danfoisy/flicker/docs/images/20191109_113527.jpg

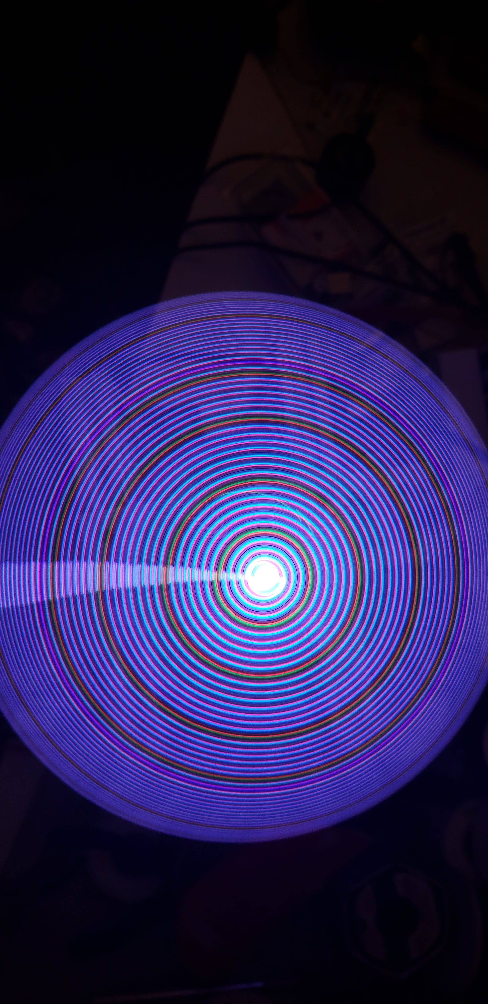
docs/images/20191109_113527.jpg
