danfoisy/flicker/prints/slots v1.stl

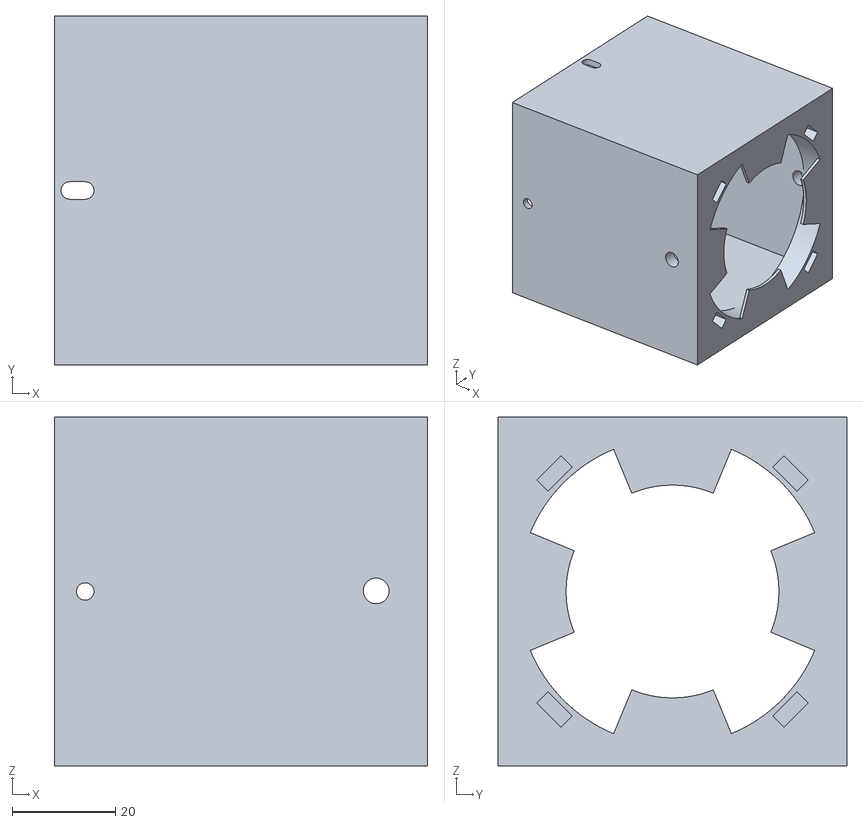
[picture p44: CAD file, 2020-12-12]
prints/slots v1.stl
72.5 x 67.8 x 67.8
