danfoisy/flicker/prints/motor magnet.stl

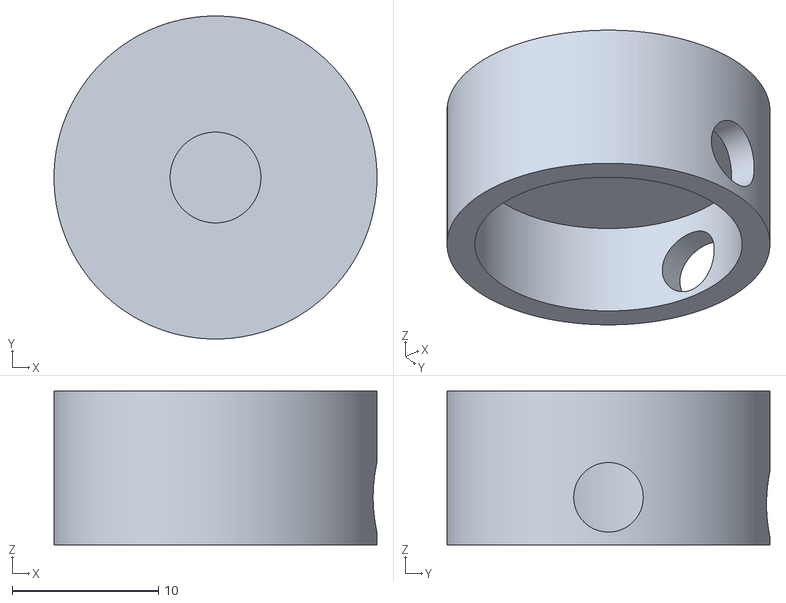
[picture p45: CAD file, 2020-12-12]
prints/motor magnet.stl
22.0 x 22.0 x 10.5
