danfoisy/flicker/prints/stand.stl

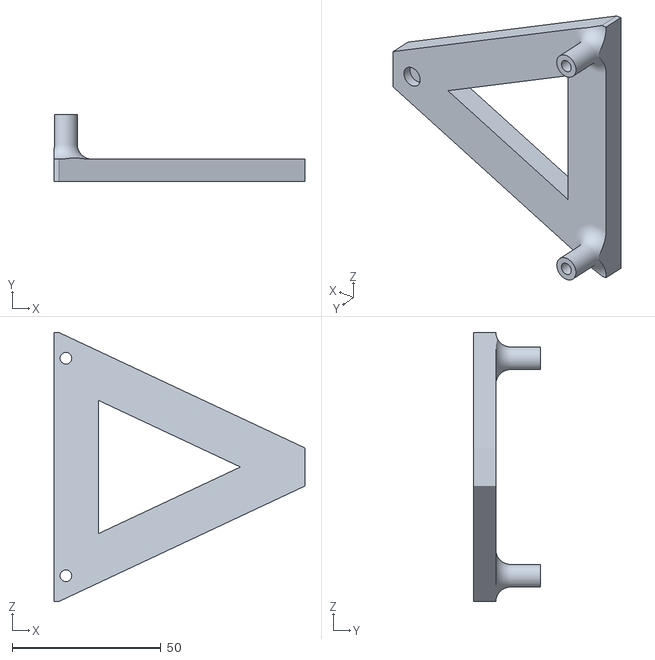
[picture p46: CAD file, 2020-12-12]
prints/stand.stl
84.3 x 22.5 x 90.4
