danfoisy/flicker/prints/counterweight.stl

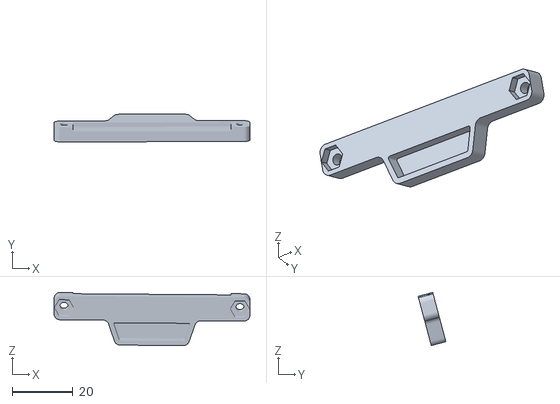
[picture p47: CAD file, 2020-12-12]
prints/counterweight.stl
64.6 x 9.18 x 17.5
