danfoisy/flicker/prints/finger holderx4a.stl

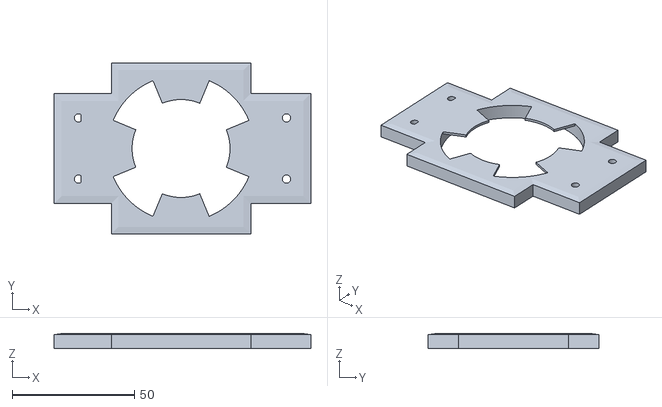
[picture p48: CAD file, 2020-12-12]
prints/finger holderx4a.stl
105.0 x 70.0 x 6.00
