danfoisy/flicker/prints/pcb_coupler v2.stl

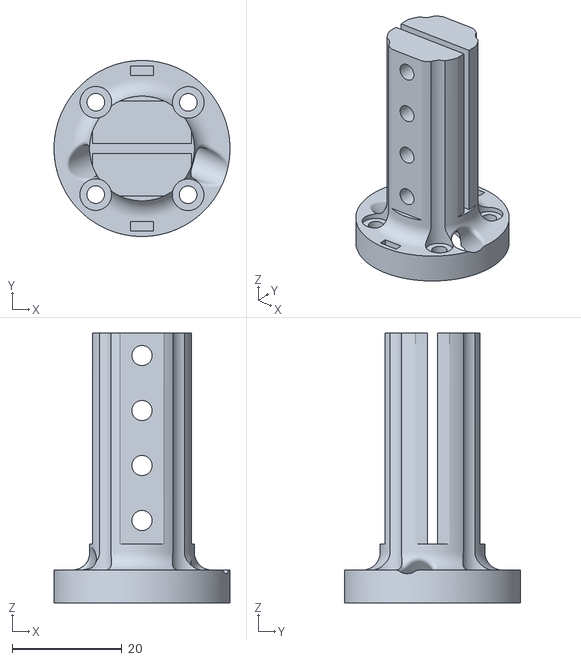
[picture p49: CAD file, 2020-12-12]
prints/pcb_coupler v2.stl
32.0 x 32.0 x 49.1
