danfoisy/flicker/prints/top spacer.stl

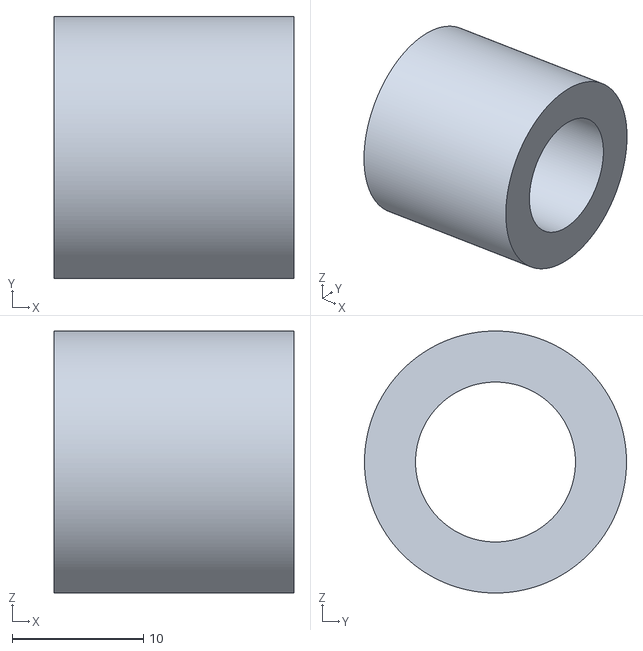
[picture p50: CAD file, 2020-12-12]
prints/top spacer.stl
18.3 x 20.0 x 20.0
