danfoisy/flicker/prints/magholder_retainer.stl

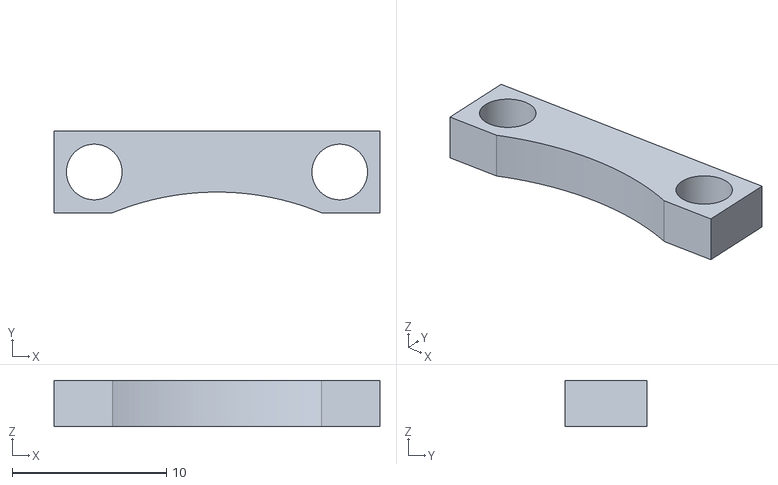
[picture p51: CAD file, 2020-12-12]
prints/magholder_retainer.stl
21.1 x 5.30 x 3.00
