danfoisy/flicker/prints/timing.stl

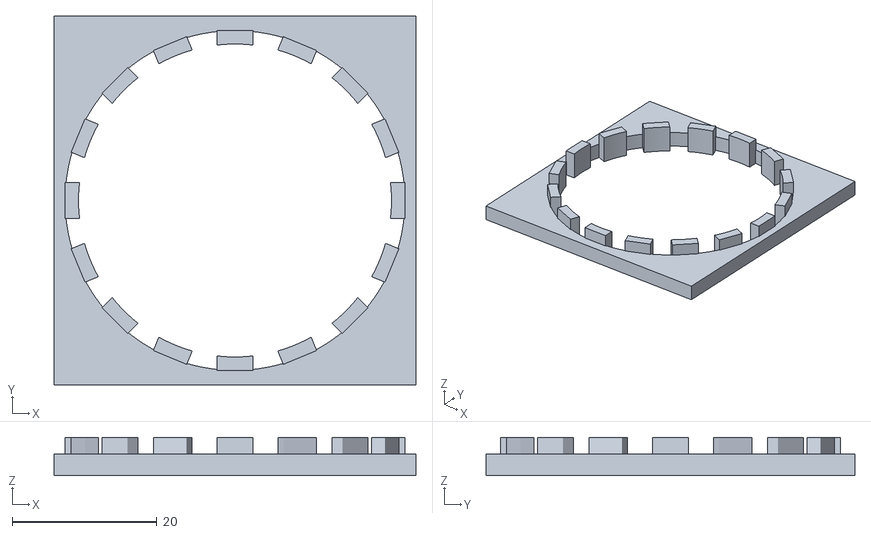
[picture p52: CAD file, 2020-12-12]
prints/timing.stl
50.0 x 51.0 x 5.28
