danfoisy/flicker/prints/bearing support.stl

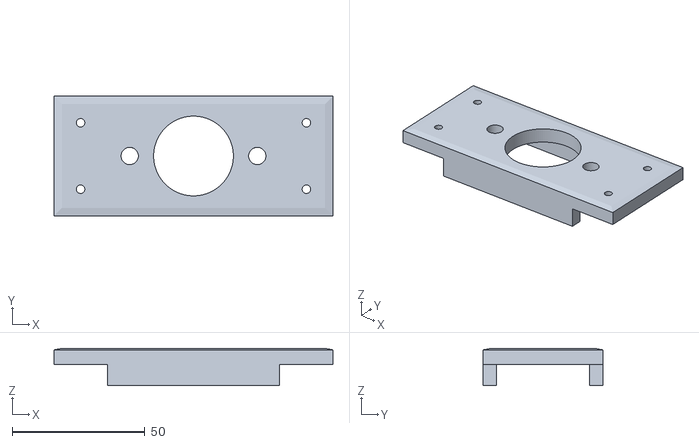
[picture p53: CAD file, 2020-12-12]
prints/bearing support.stl
105.0 x 45.0 x 14.0
