danfoisy/flicker/prints/motor mount.stl

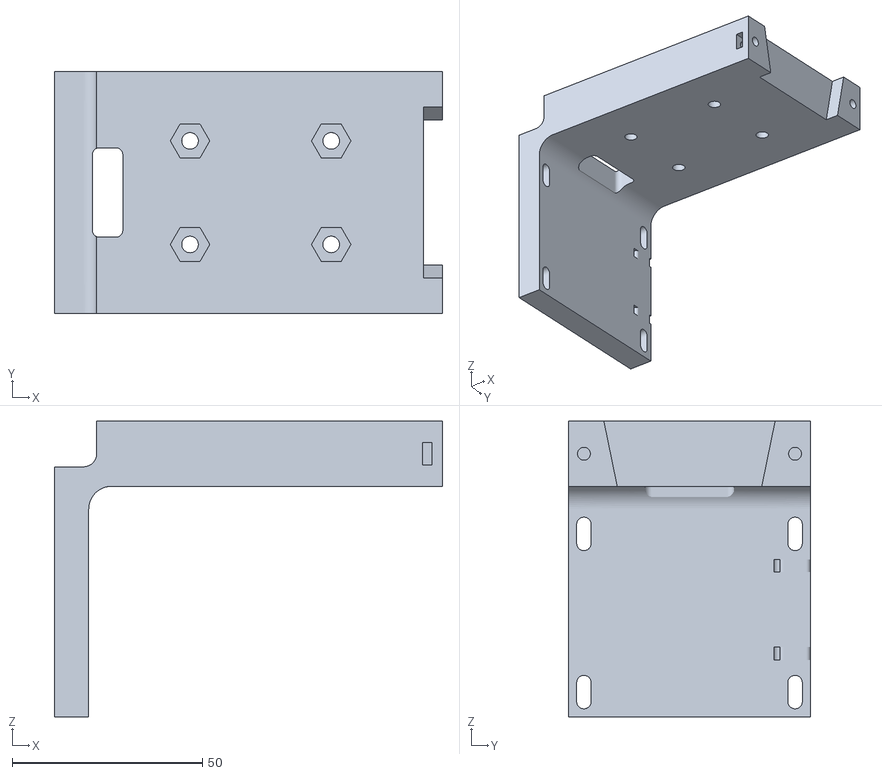
[picture p54: CAD file, 2020-12-12]
prints/motor mount.stl
102.0 x 63.5 x 77.7
