danfoisy/flicker/prints/housing top.stl

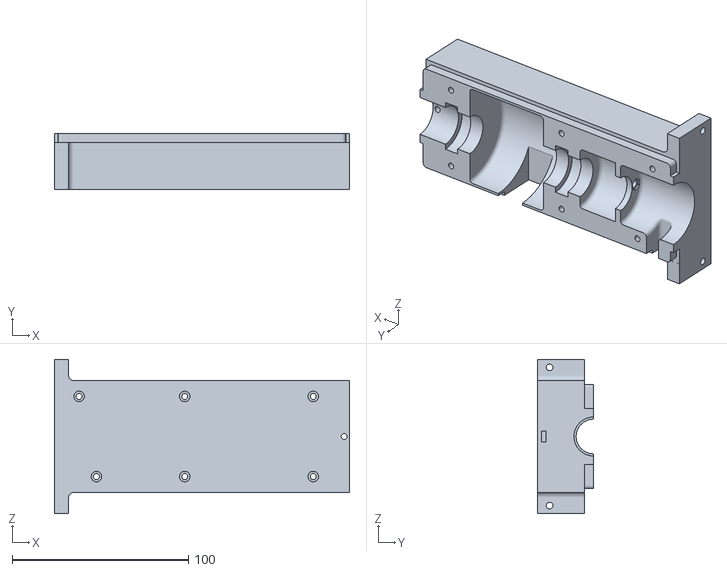
[picture p55: CAD file, 2020-12-12]
prints/housing top.stl
167.5 x 31.8 x 87.5
