danfoisy/flicker/prints/bottom spacer.stl

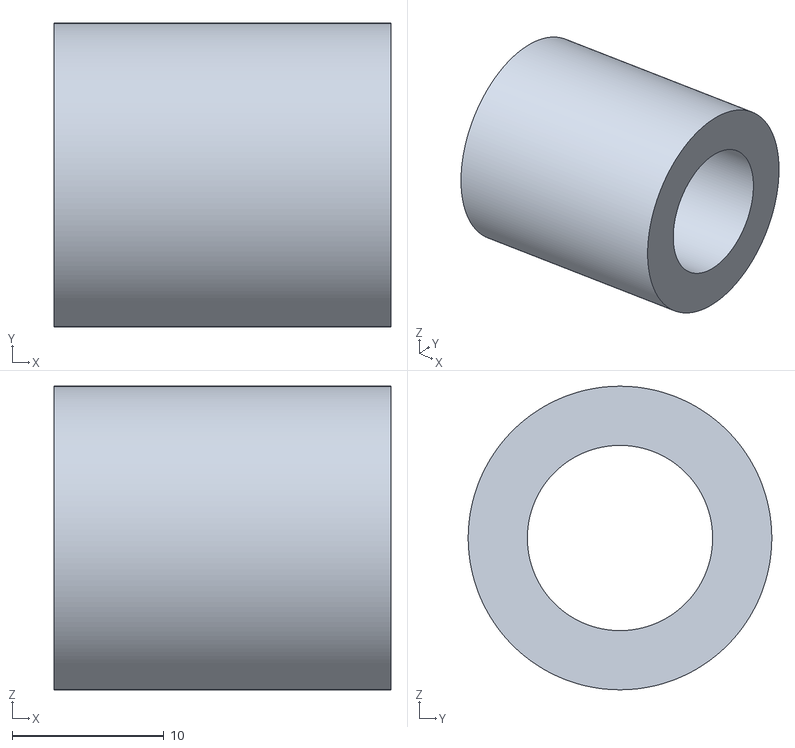
[picture p56: CAD file, 2020-12-12]
prints/bottom spacer.stl
22.2 x 20.0 x 20.0
