danfoisy/flicker/prints/slots.stl

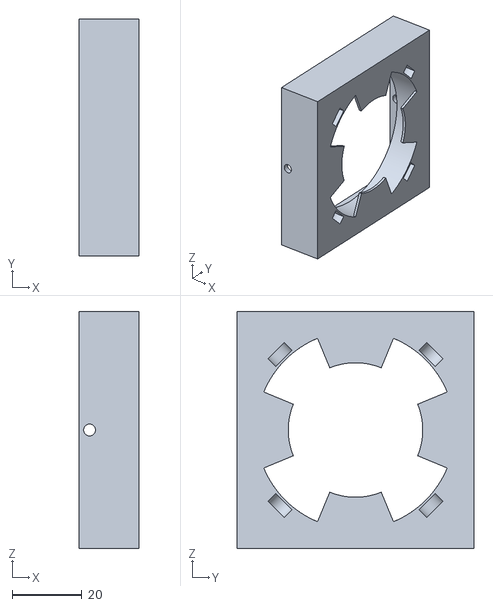
[picture p57: CAD file, 2020-12-12]
prints/slots.stl
17.1 x 67.8 x 67.8
