danfoisy/flicker/prints/finger holder.stl

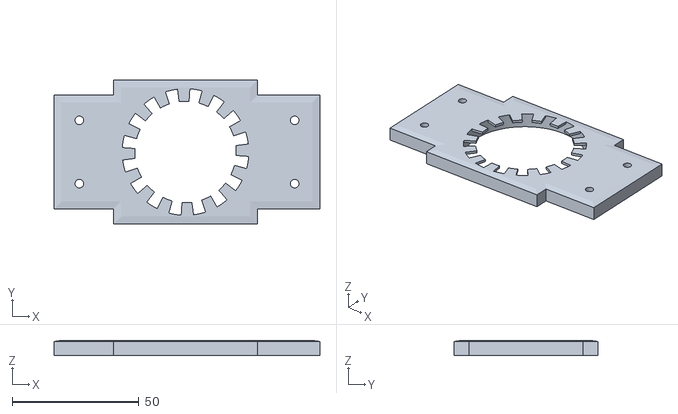
[picture p58: CAD file, 2020-12-12]
prints/finger holder.stl
105.0 x 57.0 x 6.00
