danfoisy/flicker/prints/rpm sensor holder.stl

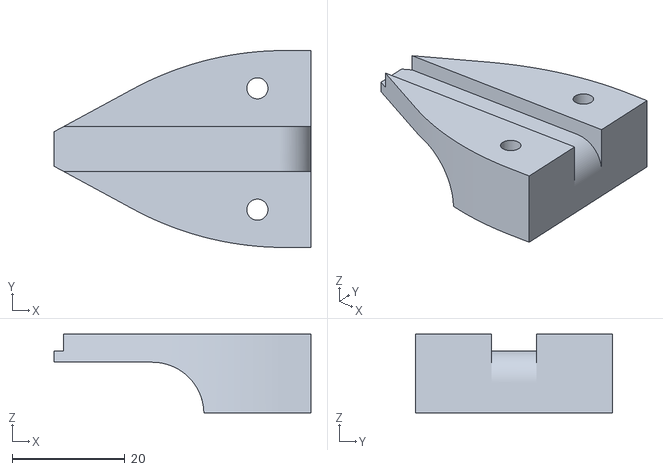
[picture p59: CAD file, 2020-12-12]
prints/rpm sensor holder.stl
45.7 x 35.0 x 14.0
