danfoisy/flicker/prints/housing bottom.stl

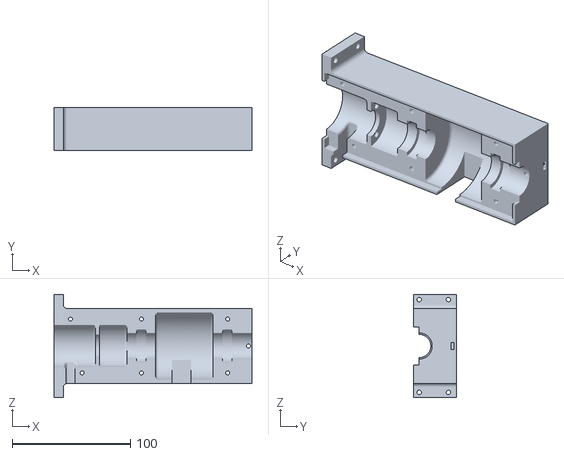
[picture p60: CAD file, 2020-12-12]
prints/housing bottom.stl
167.5 x 36.8 x 87.5
