danfoisy/flicker/prints/sensor mnt.stl

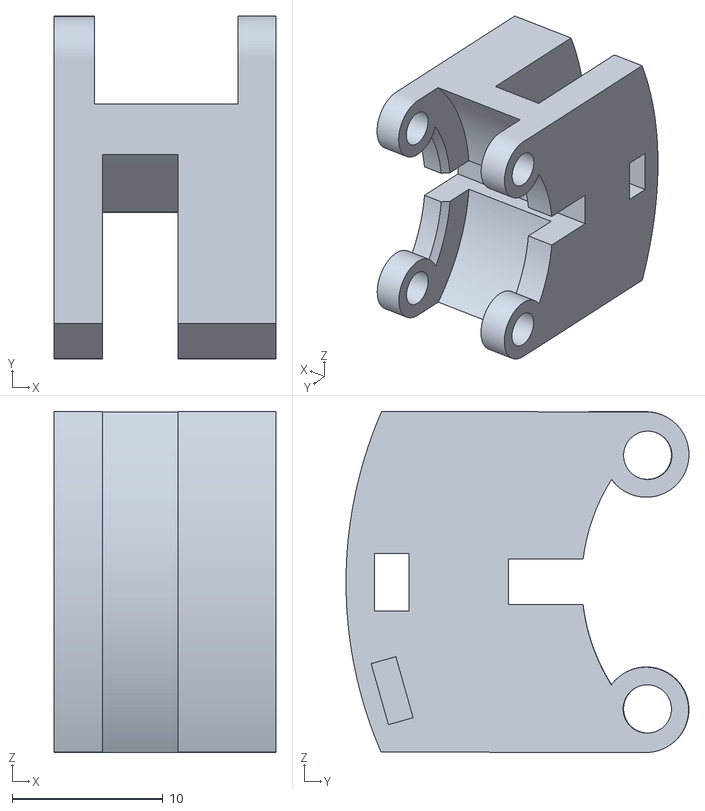
[picture p61: CAD file, 2020-12-12]
prints/sensor mnt.stl
14.7 x 22.7 x 22.6
