danfoisy/flicker/prints/weight top.stl

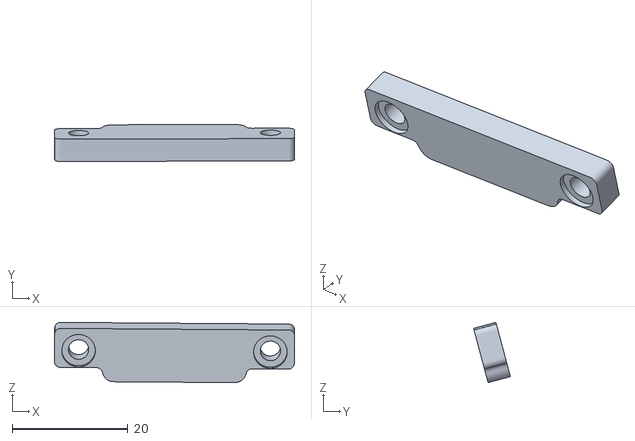
[picture p62: CAD file, 2020-12-12]
prints/weight top.stl
41.4 x 6.37 x 10.4
