danfoisy/flicker/prints/sliprng support.stl

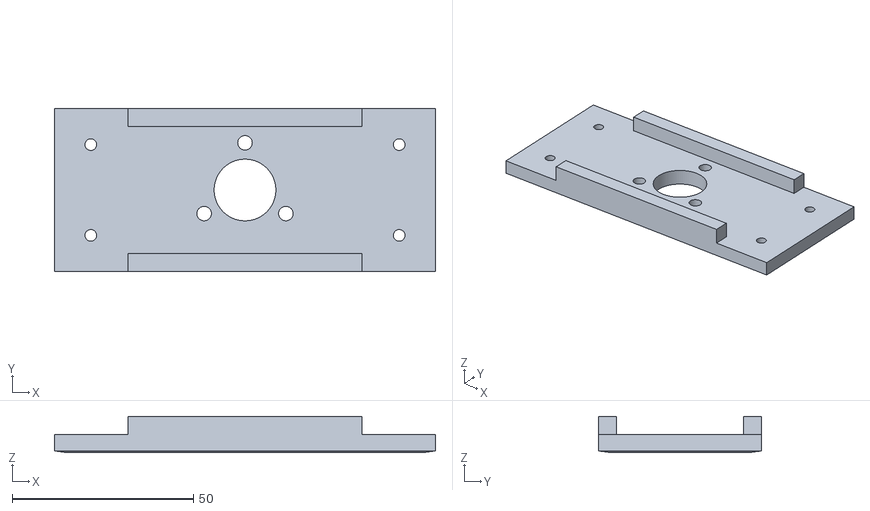
[picture p63: CAD file, 2020-12-12]
prints/sliprng support.stl
105.0 x 45.0 x 10.00
