danfoisy/flicker/prints/diffuser.stl

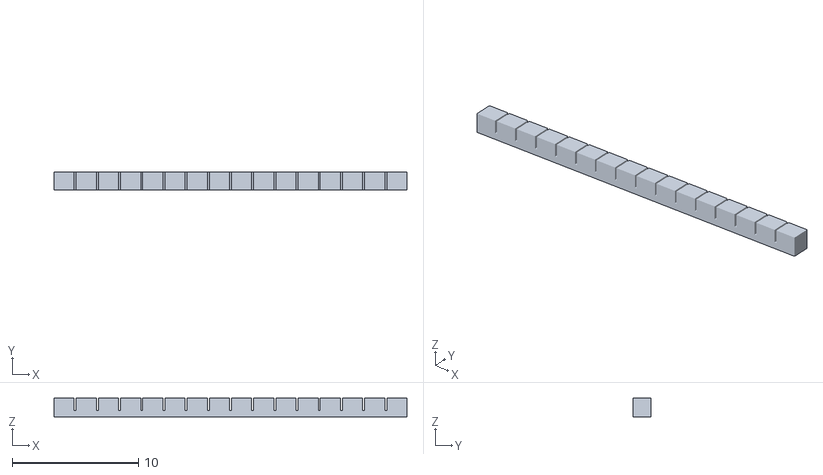
[picture p64: CAD file, 2020-12-12]
prints/diffuser.stl
28.0 x 1.41 x 1.50
