danfoisy/flicker/prints/top bracket.stl

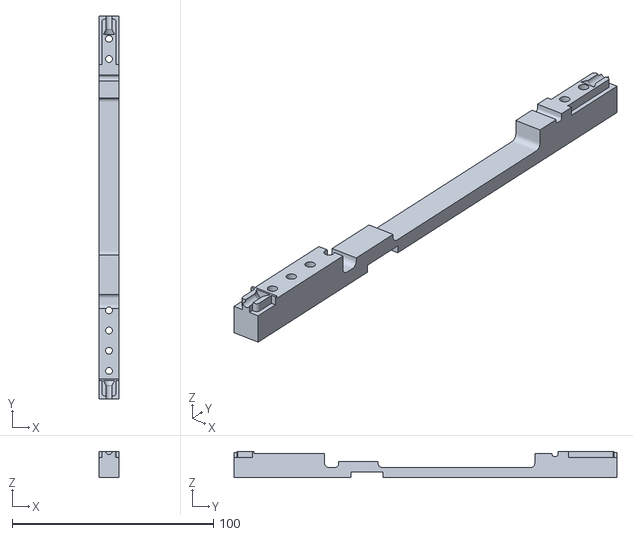
[picture p65: CAD file, 2020-12-12]
prints/top bracket.stl
10.0 x 190.1 x 12.9
