danfoisy/flicker/prints/box top.stl

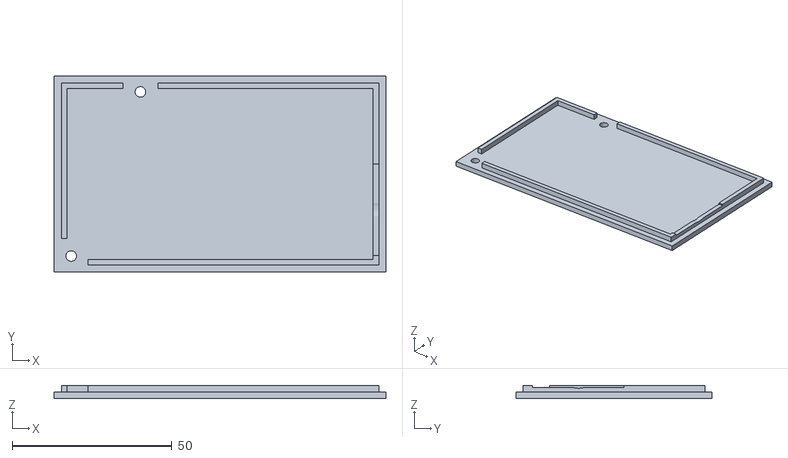
[picture p66: CAD file, 2020-12-12]
prints/box top.stl
103.9 x 61.3 x 4.00
