danfoisy/flicker/prints/magnet holder 2.stl

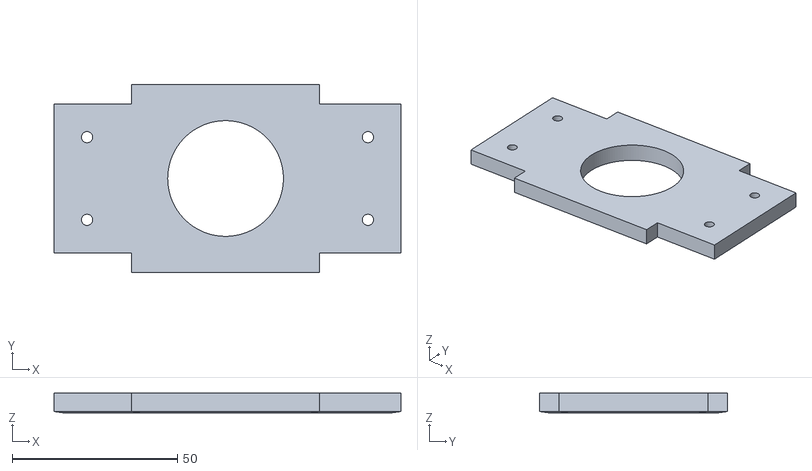
[picture p67: CAD file, 2020-12-12]
prints/magnet holder 2.stl
105.0 x 57.0 x 6.00
