danfoisy/flicker/prints/timing1.stl

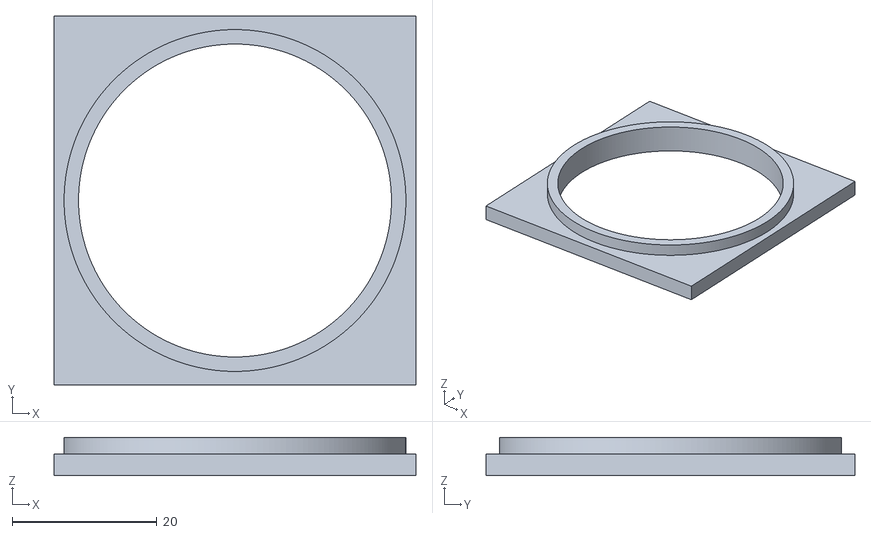
[picture p68: CAD file, 2020-12-12]
prints/timing1.stl
50.0 x 51.0 x 5.28
