danfoisy/flicker/board/flicker/200-memory.sch

## KiCad design board/flicker/200-memory.sch (2020-12-05)

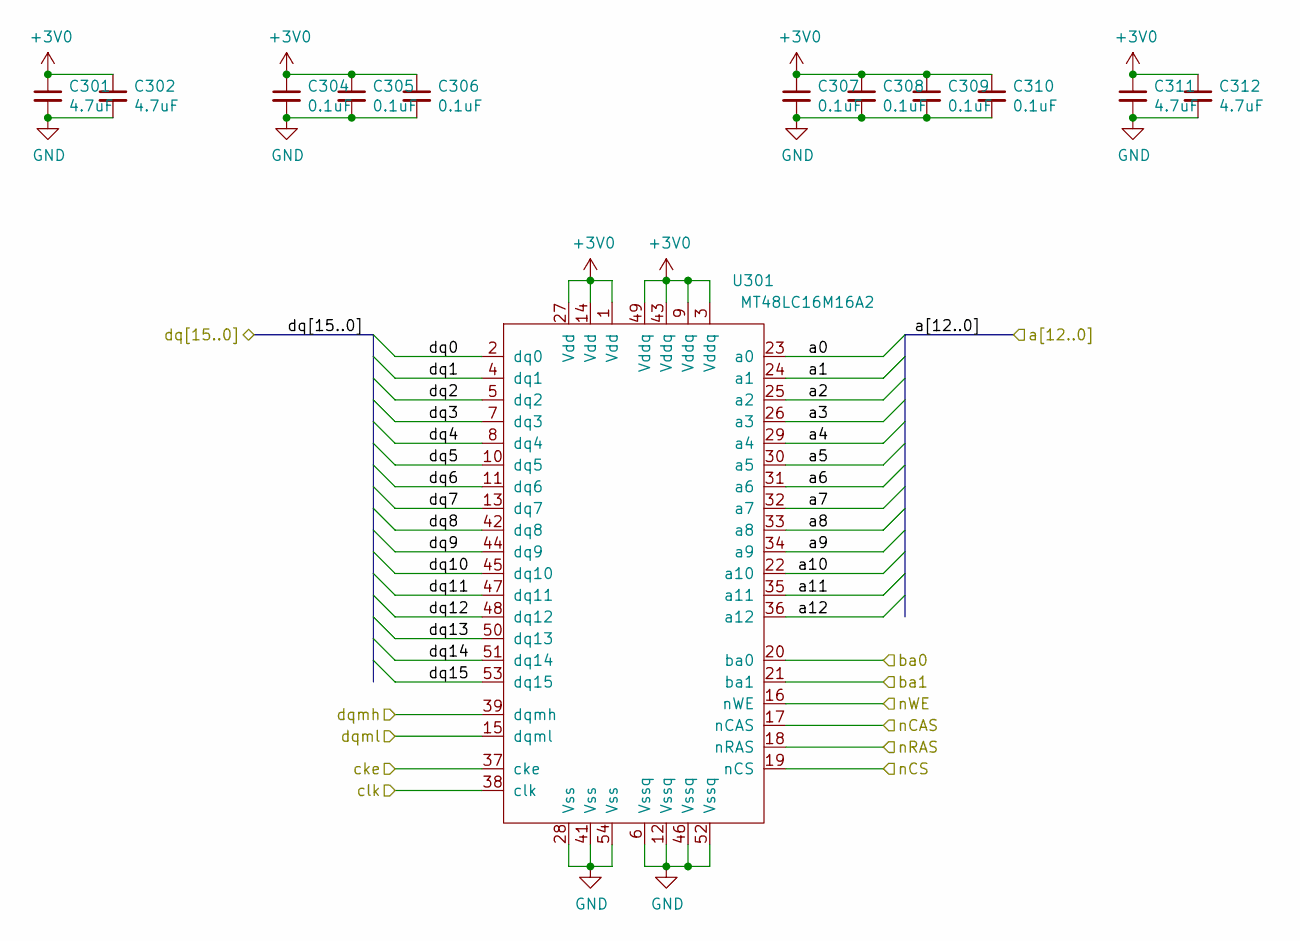
[picture p91: schematic 200-memory.sch]

Parts:
C301, C302, C311, C312: 4.7uF; C_0603_1608Metric_Pad1.05x0.95mm_HandSolder
C304, C305, C306, C307, C308, C309, C310: 0.1uF; C_0402_1005Metric_HandSolder
U301: MT48LC16M16A2; TSOP-II-54_22.2x10.16mm_P0.8mm

Connections:
+3V0: C301.1, C302.1, C304.1, C305.1, C306.1, C307.1, C308.1, C309.1, C310.1, C311.1, C312.1, U301.1 (Vdd), U301.3 (Vddq), U301.9 (Vddq), U301.14 (Vdd), U301.27 (Vdd~), U301.43 (Vddq), U301.49 (Vddq)
GND: C301.2, C302.2, C304.2, C305.2, C306.2, C307.2, C308.2, C309.2, C310.2, C311.2, C312.2, U301.6 (Vssq), U301.12 (Vssq), U301.28 (Vss), U301.41 (Vss), U301.46 (Vssq), U301.52 (Vssq), U301.54 (Vss)
a0: U301.23 (a0~)
a1: U301.24 (a1)
a2: U301.25 (a2)
a3: U301.26 (a3)
a4: U301.29 (a4)
a5: U301.30 (a5)
a6: U301.31 (a6)
a7: U301.32 (a7)
a8: U301.33 (a8)
a9: U301.34 (a9)
a10: U301.22 (a10~)
a11: U301.35 (a11)
a12: U301.36 (a12)
ba0: U301.20 (ba0~)
ba1: U301.21 (ba1)
cke: U301.37 (cke)
clk: U301.38 (clk)
dq0: U301.2 (dq0)
dq1: U301.4 (dq1)
dq2: U301.5 (dq2)
dq3: U301.7 (dq3)
dq4: U301.8 (dq4)
dq5: U301.10 (dq5)
dq6: U301.11 (dq6)
dq7: U301.13 (dq7)
dq8: U301.42 (dq8)
dq9: U301.44 (dq9)
dq10: U301.45 (dq10)
dq11: U301.47 (dq11)
dq12: U301.48 (dq12)
dq13: U301.50 (dq13)
dq14: U301.51 (dq14)
dq15: U301.53 (dq15)
dqmh: U301.39 (dqmh)
dqml: U301.15 (dqml)
nCAS: U301.17 (nCAS)
nCS: U301.19 (nCS~)
nRAS: U301.18 (nRAS)
nWE: U301.16 (nWE)
