danfoisy/flicker/board/flicker/300-HDMI.sch

## KiCad design board/flicker/300-HDMI.sch (2020-12-05)

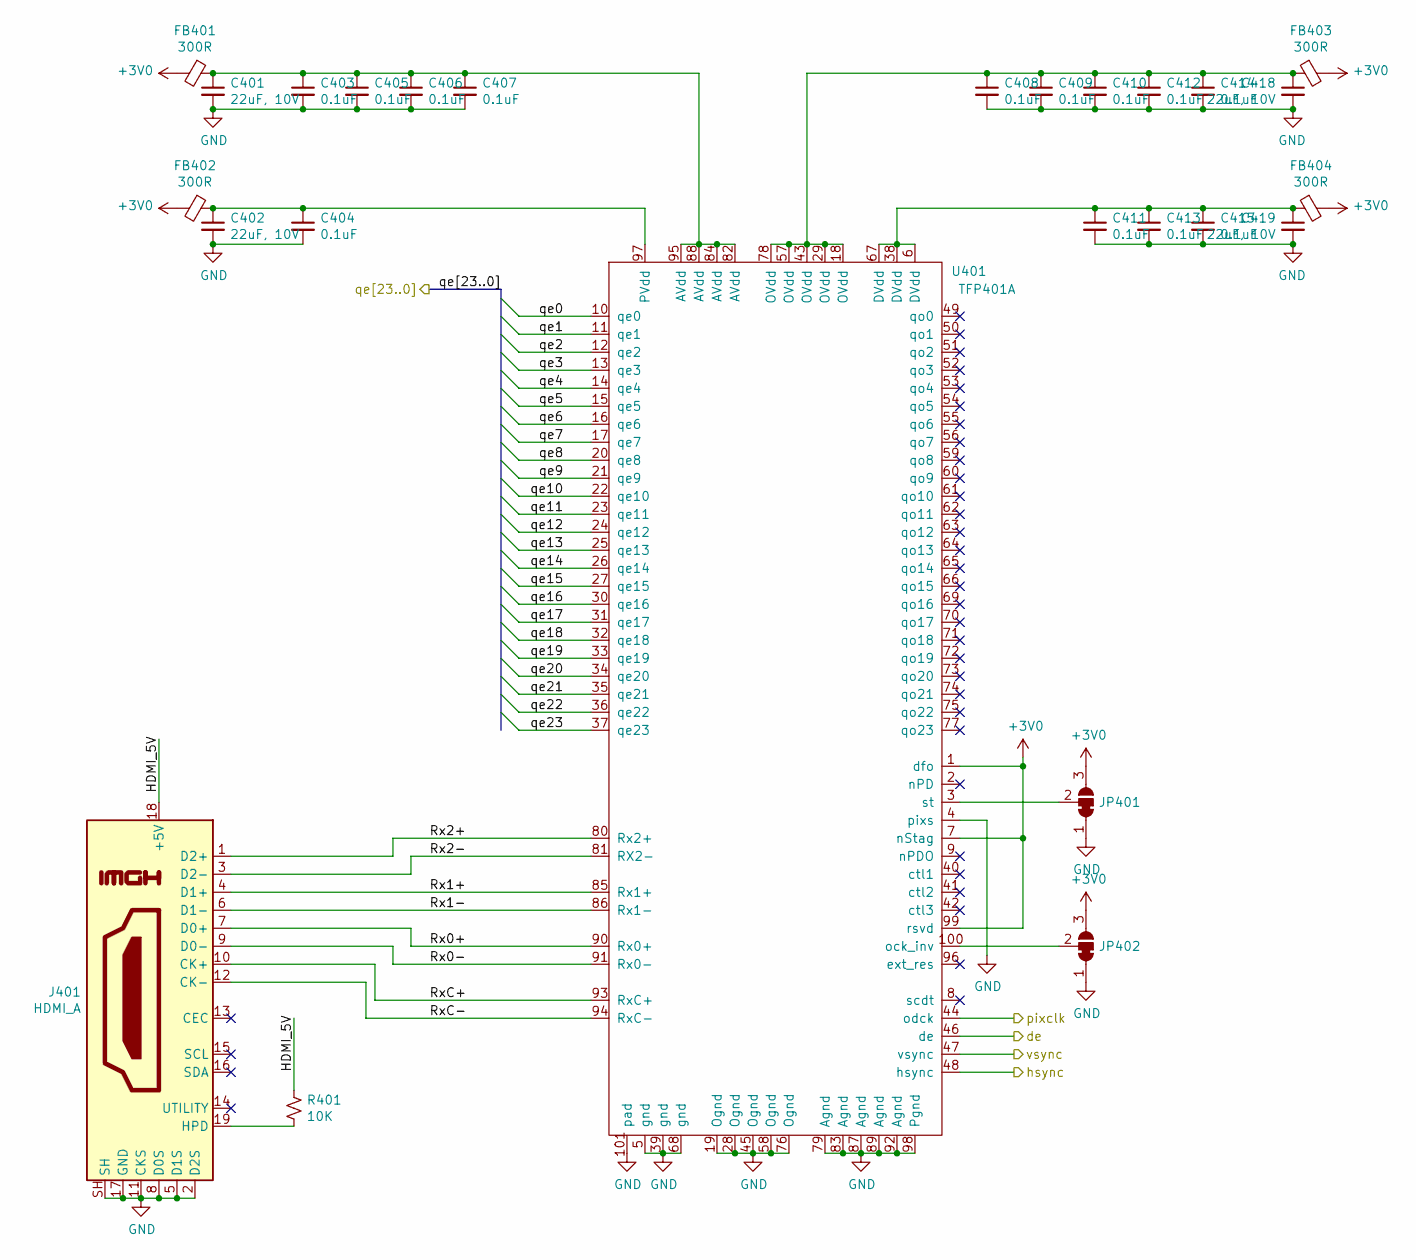
[picture p92: schematic 300-HDMI.sch]

Parts:
C401, C402, C418, C419: 22uF, 10V; C_0805_2012Metric_Pad1.15x1.40mm_HandSolder
C403, C404, C405, C406, C407, C408, C409, C410, C411, C412, C413, C414, C415: 0.1uF; C_0402_1005Metric_HandSolder
FB401, FB402, FB403, FB404: 300R; R_0402_1005Metric_HandSolder
J401: HDMI_A; HDMI_A_TE_5-1903015-5
JP401, JP402: SolderJumper_3_Bridged12; SolderJumper-3_bridged12
R401: 10K; R_0402_1005Metric_HandSolder
U401: TFP401A; TQFP-100-1EP_14x14mm_P0.5mm_EP5x5mm

Connections:
+3V0: FB401.2, FB402.2, FB403.2, FB404.2, JP401.3 (B), JP402.3 (B), U401.1 (dfo), U401.7 (nStag), U401.99 (rsvd)
GND: C401.2, C402.2, C403.2, C404.2, C405.2, C406.2, C407.2, C408.2, C409.2, C410.2, C411.2, C412.2, C413.2, C414.2, C415.2, C418.2, C419.2, J401.2 (D2S), J401.5 (D1S), J401.8 (D0S), J401.11 (CKS), J401.17 (GND), J401.SH, JP401.1 (A), JP402.1 (A), U401.4 (pixs), U401.5 (gnd), U401.19 (Ognd), U401.28 (Ognd), U401.39 (gnd), U401.45 (Ognd), U401.58 (Ognd), U401.68 (gnd), U401.76 (Ognd), U401.79 (Agnd), U401.83 (Agnd), U401.87 (Agnd), U401.89 (Agnd), U401.92 (Agnd), U401.98 (Pgnd), U401.101 (pad)
HDMI_5V: J401.18 (+5V), R401.1
unnamed: C401.1, C403.1, C405.1, C406.1, C407.1, FB401.1, U401.82 (AVdd), U401.84 (AVdd), U401.88 (AVdd), U401.95 (AVdd)
unnamed: C402.1, C404.1, FB402.1, U401.97 (PVdd)
unnamed: C408.1, C409.1, C410.1, C412.1, C414.1, C418.1, FB403.1, U401.18 (OVdd~), U401.29 (OVdd), U401.43 (OVdd), U401.57 (OVdd), U401.78 (OVdd)
unnamed: C411.1, C413.1, C415.1, C419.1, FB404.1, U401.6 (DVdd), U401.38 (DVdd), U401.67 (DVdd)
unnamed: J401.19 (HPD), R401.2
unnamed: JP401.2 (C), U401.3 (st)
unnamed: JP402.2 (C), U401.100 (ock_inv)
Rx0+: J401.7 (D0+), U401.90 (Rx0+)
Rx0-: J401.9 (D0-), U401.91 (Rx0-)
Rx1+: J401.4 (D1+), U401.85 (Rx1+)
Rx1-: J401.6 (D1-), U401.86 (Rx1-)
Rx2+: J401.1 (D2+), U401.80 (Rx2+)
Rx2-: J401.3 (D2-), U401.81 (RX2-)
RxC+: J401.10 (CK+), U401.93 (RxC+)
RxC-: J401.12 (CK-), U401.94 (RxC-)
de: U401.46 (de~)
hsync: U401.48 (hsync)
pixclk: U401.44 (odck)
qe0: U401.10 (qe0)
qe1: U401.11 (qe1)
qe2: U401.12 (qe2)
qe3: U401.13 (qe3)
qe4: U401.14 (qe4)
qe5: U401.15 (qe5)
qe6: U401.16 (qe6)
qe7: U401.17 (qe7)
qe8: U401.20 (qe8)
qe9: U401.21 (qe9)
qe10: U401.22 (qe10)
qe11: U401.23 (qe11)
qe12: U401.24 (qe12)
qe13: U401.25 (qe13)
qe14: U401.26 (qe14)
qe15: U401.27 (qe15)
qe16: U401.30 (qe16)
qe17: U401.31 (qe17)
qe18: U401.32 (qe18)
qe19: U401.33 (qe19)
qe20: U401.34 (qe20)
qe21: U401.35 (qe21)
qe22: U401.36 (qe22)
qe23: U401.37 (qe23)
vsync: U401.47 (vsync)
