danfoisy/flicker/board/flicker/LED.sch

## KiCad design board/flicker/LED.sch (2020-12-05)

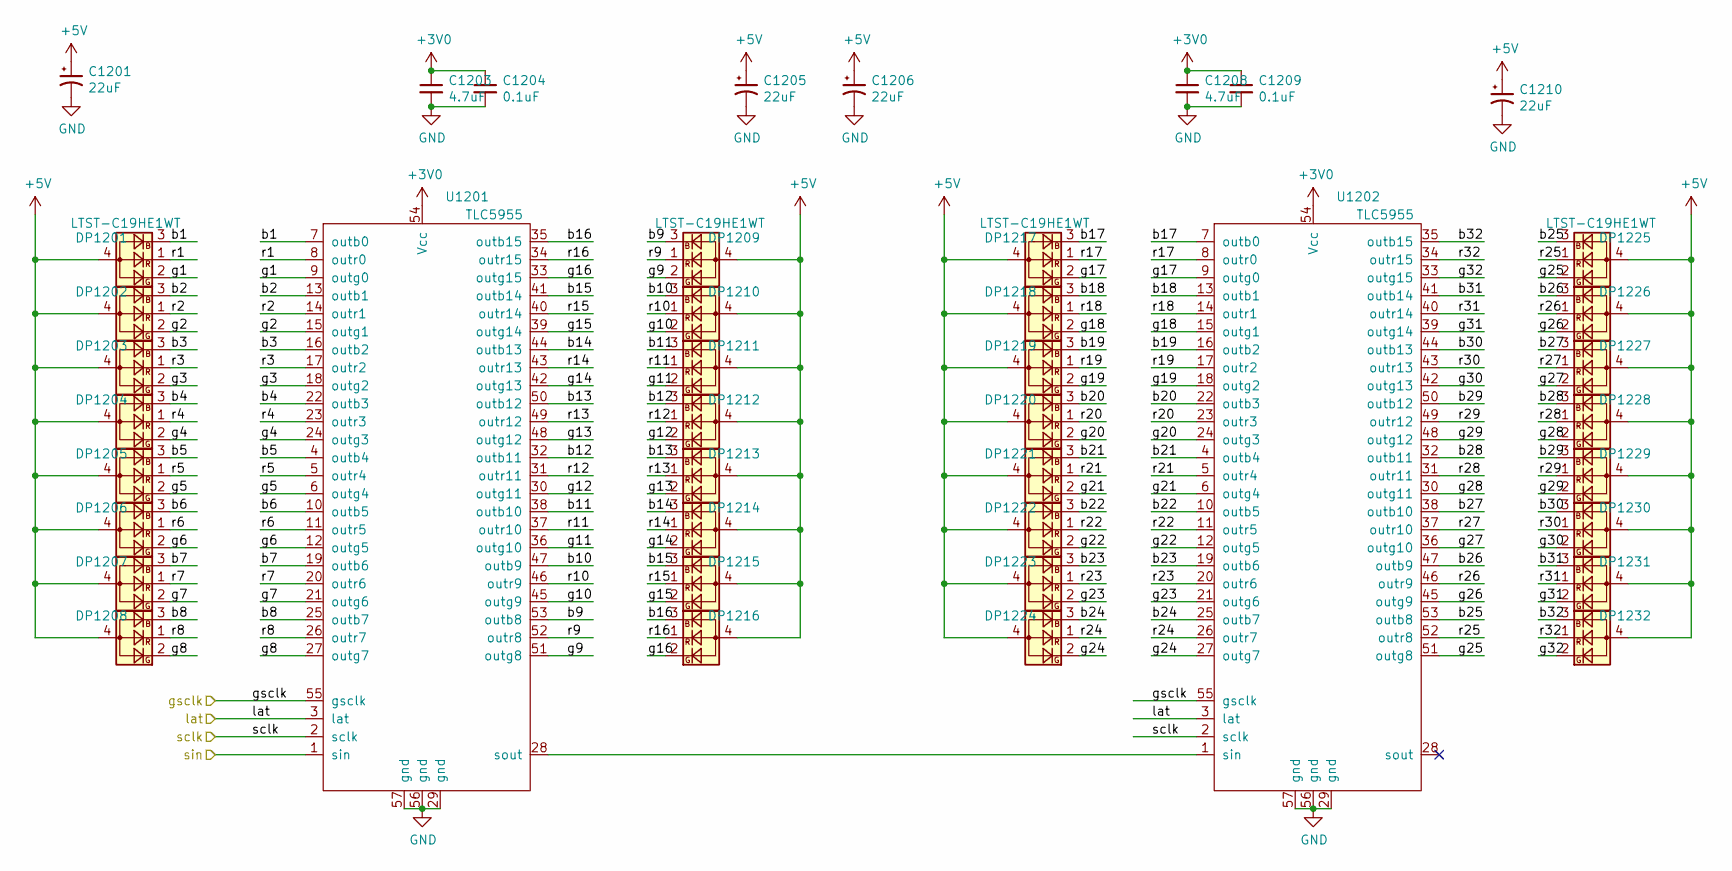
[picture p93: schematic LED.sch]

Parts:
C501, C505, C506, C510: 22uF; CP_Elec_4x5.4
C503, C508: 4.7uF; C_0603_1608Metric_Pad1.05x0.95mm_HandSolder
C504, C509: 0.1uF; C_0402_1005Metric_HandSolder
DP501, DP502, DP503, DP504, DP505, DP506, DP507, DP508, DP509, DP510, DP511, DP512, DP513, DP514, DP515, DP516, DP517, DP518, DP519, DP520, DP521, DP522, DP523, DP524, DP525, DP526, DP527, DP528, DP529, DP530, DP531, DP532: LTST-C19HE1WT
U501, U502: TLC5955; HTSSOP-56-1EP_6.1x14mm_P0.5mm_EP3.61x4.7mm

Connections:
+3V0: C503.1, C504.1, C508.1, C509.1, U501.54 (Vcc), U502.54 (Vcc)
+5V: C501.1, C505.1, C506.1, C510.1, DP501.4 (A), DP502.4 (A), DP503.4 (A), DP504.4 (A), DP505.4 (A), DP506.4 (A), DP507.4 (A), DP508.4 (A), DP509.4 (A), DP510.4 (A), DP511.4 (A), DP512.4 (A), DP513.4 (A), DP514.4 (A), DP515.4 (A), DP516.4 (A), DP517.4 (A), DP518.4 (A), DP519.4 (A), DP520.4 (A), DP521.4 (A), DP522.4 (A), DP523.4 (A), DP524.4 (A), DP525.4 (A), DP526.4 (A), DP527.4 (A), DP528.4 (A), DP529.4 (A), DP530.4 (A), DP531.4 (A), DP532.4 (A)
GND: C501.2, C503.2, C504.2, C505.2, C506.2, C508.2, C509.2, C510.2, U501.29 (gnd), U501.56 (gnd), U501.57 (gnd), U502.29 (gnd), U502.56 (gnd), U502.57 (gnd)
unnamed: U501.28 (sout), U502.1 (sin)
b1: DP501.3 (RK), U501.7 (outb0)
b2: DP502.3 (RK), U501.13 (outb1)
b3: DP503.3 (RK), U501.16 (outb2)
b4: DP504.3 (RK), U501.22 (outb3)
b5: DP505.3 (RK), U501.4 (outb4)
b6: DP506.3 (RK), U501.10 (outb5)
b7: DP507.3 (RK), U501.19 (outb6)
b8: DP508.3 (RK), U501.25 (outb7)
b9: DP509.3 (RK), U501.53 (outb8)
b10: DP510.3 (RK), U501.47 (outb9)
b11: DP511.3 (RK), U501.38 (outb10)
b12: DP512.3 (RK), U501.32 (outb11)
b13: DP513.3 (RK), U501.50 (outb12)
b14: DP514.3 (RK), U501.44 (outb13)
b15: DP515.3 (RK), U501.41 (outb14)
b16: DP516.3 (RK), U501.35 (outb15)
b17: DP517.3 (RK), U502.7 (outb0)
b18: DP518.3 (RK), U502.13 (outb1)
b19: DP519.3 (RK), U502.16 (outb2)
b20: DP520.3 (RK), U502.22 (outb3)
b21: DP521.3 (RK), U502.4 (outb4)
b22: DP522.3 (RK), U502.10 (outb5)
b23: DP523.3 (RK), U502.19 (outb6)
b24: DP524.3 (RK), U502.25 (outb7)
b25: DP525.3 (RK), U502.53 (outb8)
b26: DP526.3 (RK), U502.47 (outb9)
b27: DP527.3 (RK), U502.38 (outb10)
b28: DP528.3 (RK), U502.32 (outb11)
b29: DP529.3 (RK), U502.50 (outb12)
b30: DP530.3 (RK), U502.44 (outb13)
b31: DP531.3 (RK), U502.41 (outb14)
b32: DP532.3 (RK), U502.35 (outb15)
g1: DP501.2 (BK), U501.9 (outg0)
g2: DP502.2 (BK), U501.15 (outg1)
g3: DP503.2 (BK), U501.18 (outg2)
g4: DP504.2 (BK), U501.24 (outg3)
g5: DP505.2 (BK), U501.6 (outg4)
g6: DP506.2 (BK), U501.12 (outg5)
g7: DP507.2 (BK), U501.21 (outg6)
g8: DP508.2 (BK), U501.27 (outg7)
g9: DP509.2 (BK), U501.51 (outg8)
g10: DP510.2 (BK), U501.45 (outg9)
g11: DP511.2 (BK), U501.36 (outg10)
g12: DP512.2 (BK), U501.30 (outg11)
g13: DP513.2 (BK), U501.48 (outg12)
g14: DP514.2 (BK), U501.42 (outg13)
g15: DP515.2 (BK), U501.39 (outg14)
g16: DP516.2 (BK), U501.33 (outg15)
g17: DP517.2 (BK), U502.9 (outg0)
g18: DP518.2 (BK), U502.15 (outg1)
g19: DP519.2 (BK), U502.18 (outg2)
g20: DP520.2 (BK), U502.24 (outg3)
g21: DP521.2 (BK), U502.6 (outg4)
g22: DP522.2 (BK), U502.12 (outg5)
g23: DP523.2 (BK), U502.21 (outg6)
g24: DP524.2 (BK), U502.27 (outg7)
g25: DP525.2 (BK), U502.51 (outg8)
g26: DP526.2 (BK), U502.45 (outg9)
g27: DP527.2 (BK), U502.36 (outg10)
g28: DP528.2 (BK), U502.30 (outg11)
g29: DP529.2 (BK), U502.48 (outg12)
g30: DP530.2 (BK), U502.42 (outg13)
g31: DP531.2 (BK), U502.39 (outg14)
g32: DP532.2 (BK), U502.33 (outg15)
gsclk: U501.55 (gsclk), U502.55 (gsclk)
lat: U501.3 (lat), U502.3 (lat)
r1: DP501.1 (GK), U501.8 (outr0)
r2: DP502.1 (GK), U501.14 (outr1)
r3: DP503.1 (GK), U501.17 (outr2)
r4: DP504.1 (GK), U501.23 (outr3)
r5: DP505.1 (GK), U501.5 (outr4)
r6: DP506.1 (GK), U501.11 (outr5)
r7: DP507.1 (GK), U501.20 (outr6)
r8: DP508.1 (GK), U501.26 (outr7)
r9: DP509.1 (GK), U501.52 (outr8)
r10: DP510.1 (GK), U501.46 (outr9)
r11: DP511.1 (GK), U501.37 (outr10)
r12: DP512.1 (GK), U501.31 (outr11)
r13: DP513.1 (GK), U501.49 (outr12)
r14: DP514.1 (GK), U501.43 (outr13)
r15: DP515.1 (GK), U501.40 (outr14)
r16: DP516.1 (GK), U501.34 (outr15)
r17: DP517.1 (GK), U502.8 (outr0)
r18: DP518.1 (GK), U502.14 (outr1)
r19: DP519.1 (GK), U502.17 (outr2)
r20: DP520.1 (GK), U502.23 (outr3)
r21: DP521.1 (GK), U502.5 (outr4)
r22: DP522.1 (GK), U502.11 (outr5)
r23: DP523.1 (GK), U502.20 (outr6)
r24: DP524.1 (GK), U502.26 (outr7)
r25: DP525.1 (GK), U502.52 (outr8)
r26: DP526.1 (GK), U502.46 (outr9)
r27: DP527.1 (GK), U502.37 (outr10)
r28: DP528.1 (GK), U502.31 (outr11)
r29: DP529.1 (GK), U502.49 (outr12)
r30: DP530.1 (GK), U502.43 (outr13)
r31: DP531.1 (GK), U502.40 (outr14)
r32: DP532.1 (GK), U502.34 (outr15)
sclk: U501.2 (sclk), U502.2 (sclk)
sin: U501.1 (sin)
