danfoisy/flicker/board/flicker/raspberrypi.sch

## KiCad design board/flicker/raspberrypi.sch (2020-12-05)

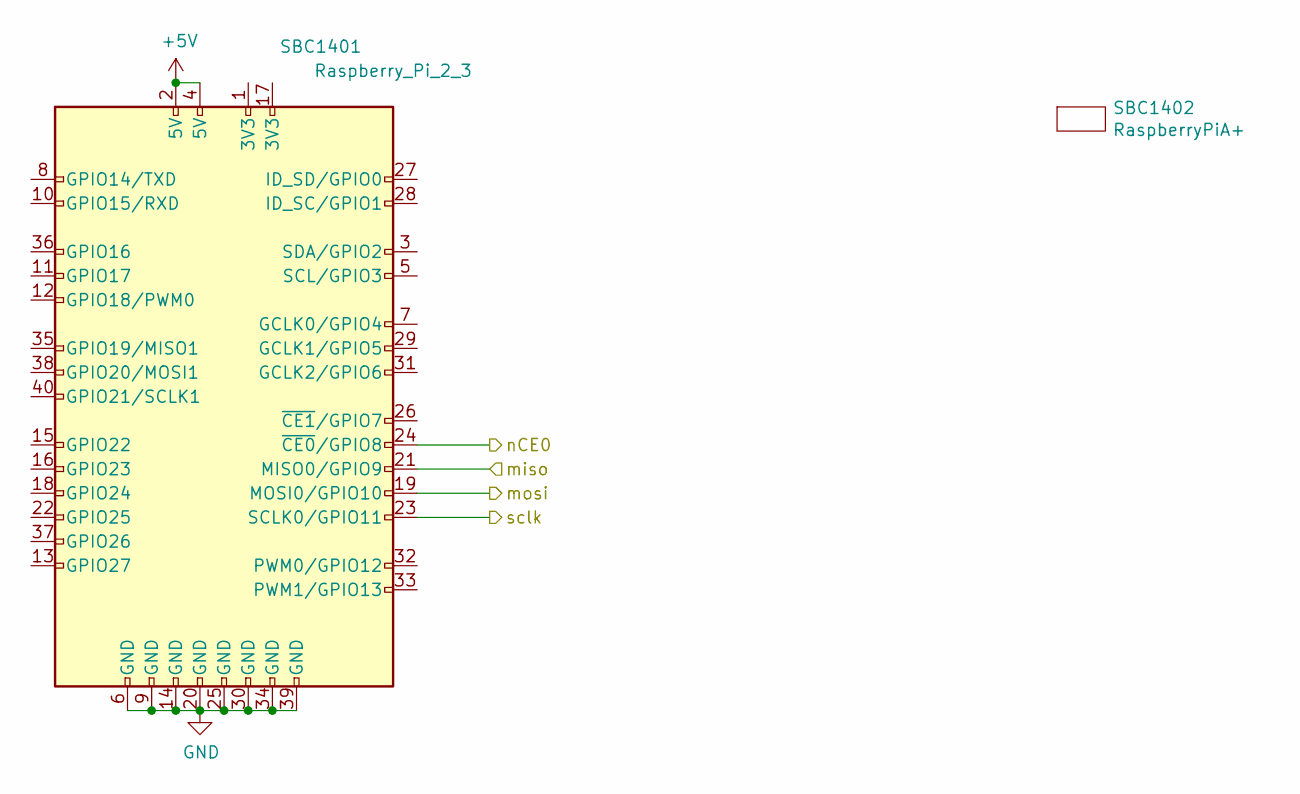
[picture p94: schematic raspberrypi.sch]

Parts:
SBC1401: Raspberry_Pi_2_3; Raspberry_Pi_Zero_Socketed_THT_MountingHoles
SBC1402: RaspberryPiA+; RaspberryPi3A+

Connections:
+5V: SBC1401.2 (5V), SBC1401.4 (5V)
GND: SBC1401.6 (GND), SBC1401.9 (GND), SBC1401.14 (GND), SBC1401.20 (GND), SBC1401.25 (GND), SBC1401.30 (GND), SBC1401.34 (GND), SBC1401.39 (GND)
miso: SBC1401.21 (MISO0/GPIO9)
mosi: SBC1401.19 (MOSI0/GPIO10)
nCE0: SBC1401.24 (~CE0~/GPIO8)
sclk: SBC1401.23 (SCLK0/GPIO11)
