danfoisy/flicker/FPGA/TurnTimer.sv

module TurnTimer #(CLK_FREQ, FPS, IMG_HEIGHT) (
		input clk,
		input nReset,
		
		input mag,
		
		output reg [$clog2(IMG_HEIGHT)-1:0] row,
		output reg [$clog2(IMG_HEIGHT)-1:0] rowEven,
		output reg valid,
		output reg index,
		output reg rowChange,
		input rowChangeAck
	);
	
	localparam NUM_MAG = 8;
	reg [$clog2(NUM_MAG)-1 : 0] magIdx;
	
	reg [3:0] i_state;
	reg [$clog2(CLK_FREQ/FPS)*2 -1 : 0] cnt;

	reg error;
	reg [$clog2(CLK_FREQ/IMG_HEIGHT)*2 -1 : 0] step;
	reg [$clog2(CLK_FREQ/IMG_HEIGHT)*2 -1 : 0] nextStep;
	
	reg [$clog2(CLK_FREQ/IMG_HEIGHT)*2 -1 : 0] stepCnt;

	
	reg magChange;
	reg oldMag;
	reg magValid;
	
	reg rowChange1;
	
	always_ff@(posedge clk) begin
		if(!nReset) begin
			magChange <= '0;
			oldMag <= mag;
			magIdx <= '1;
			magValid <= '0;
		end else begin
			magChange <= '0;
			if(oldMag != mag ) begin
				magValid <= '1;
				magChange <= '1;
				magIdx <= magIdx + 1;
			end
			oldMag <= mag;
		end
	end
	
	always_ff@(posedge clk) begin
		if(!nReset) begin
			rowChange <= '0;
		end else begin
			if(rowChange1 && !rowChange)
				rowChange <= '1;
			else if(rowChangeAck && rowChange)
				rowChange <= '0;
		end
	end
	
	always_ff@(posedge clk) begin
		if(!nReset) begin
			row <= '0;
			rowEven <= IMG_HEIGHT/2;
			stepCnt <= 1;
			index <= '0;
			rowChange1 <= '0;
		end else begin
			if(valid) begin
				index <= '0;
				rowChange1 <= '0;
			
				if(magChange && magIdx == '0) begin
					stepCnt <= 1;
					row <= 0;
					rowEven <= IMG_HEIGHT/2;
					index <= '1;
					rowChange1 <= '1; 
				end else begin
					stepCnt <= stepCnt + 1;
					
					if(stepCnt >= step) begin
						if(row < IMG_HEIGHT-1) begin
							row <=  row + 1;
							rowEven <=  rowEven + 1;
							rowChange1 <= '1;
						end else begin
							row <= IMG_HEIGHT-1;
							rowEven <= (IMG_HEIGHT/2) -1; 
						end
						
						stepCnt <= 1;
						//step <= nextStep;
					end 
				end
			end else begin 
				row <= '0;
				stepCnt <= '0;
			end

		end
	end
	

	always_ff@(posedge clk) begin: TURN_FSM
		if(!nReset) begin
			i_state <= 4'd0;
			cnt <= '0;
			error <= '1;

		end else begin
			case (i_state)
				4'd0:	
					begin
						valid <= '0;
						if(magValid && magChange) begin
							cnt <= 0;
							i_state <= 4'd3;
						end
					end
				
				4'd3:
					begin
						cnt <= cnt + 1'd1;
						
						if(cnt == CLK_FREQ/FPS*2 - 1) begin
							error <= '1;
							i_state <= 4'd0;
						end else if(magChange) begin
					
							cnt <= '0;
							error <= '0;
							
							valid <= '1;
							step <= cnt >> ($clog2(IMG_HEIGHT) - $clog2(NUM_MAG));
							
						end
						
					end
				default:
					i_state <= '0;
			endcase
		end
	end	
endmodule
	
