danfoisy/flicker/FPGA/pll/Pll_inst.v

	Pll u0 (
		.clk_in_clk    (<connected-to-clk_in_clk>),    //    clk_in.clk
		.clk_rst_reset (<connected-to-clk_rst_reset>), //   clk_rst.reset
		.gsclk_clk     (<connected-to-gsclk_clk>),     //     gsclk.clk
		.sclk_x2_clk   (<connected-to-sclk_x2_clk>),   //   sclk_x2.clk
		.sdram_clk_clk (<connected-to-sdram_clk_clk>)  // sdram_clk.clk
	);
